ixxoid/dactyl-keyboard/resources/keyb_complete_dsa_01_1.jpg

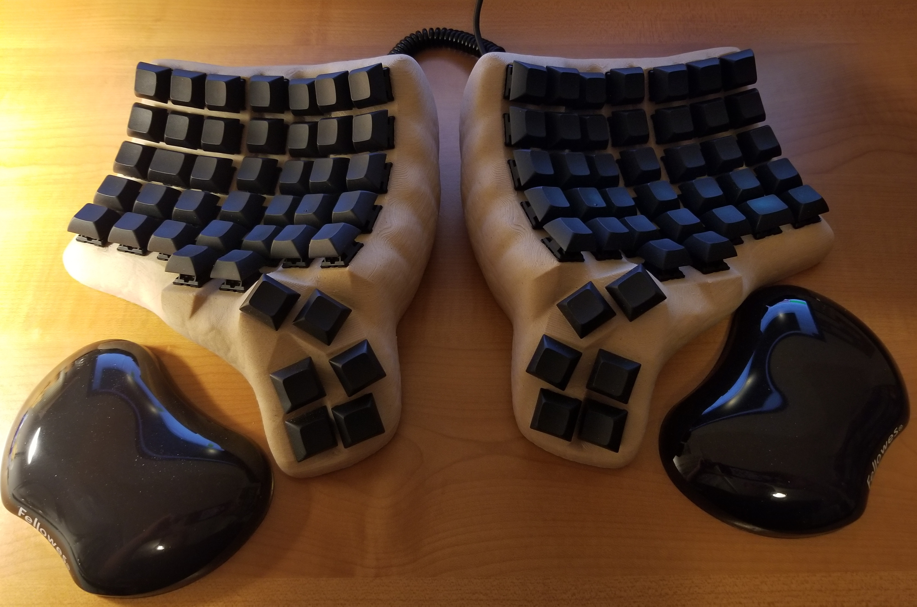
resources/keyb_complete_dsa_01_1.jpg
