ixxoid/dactyl-keyboard/resources/low_profile_preview.png

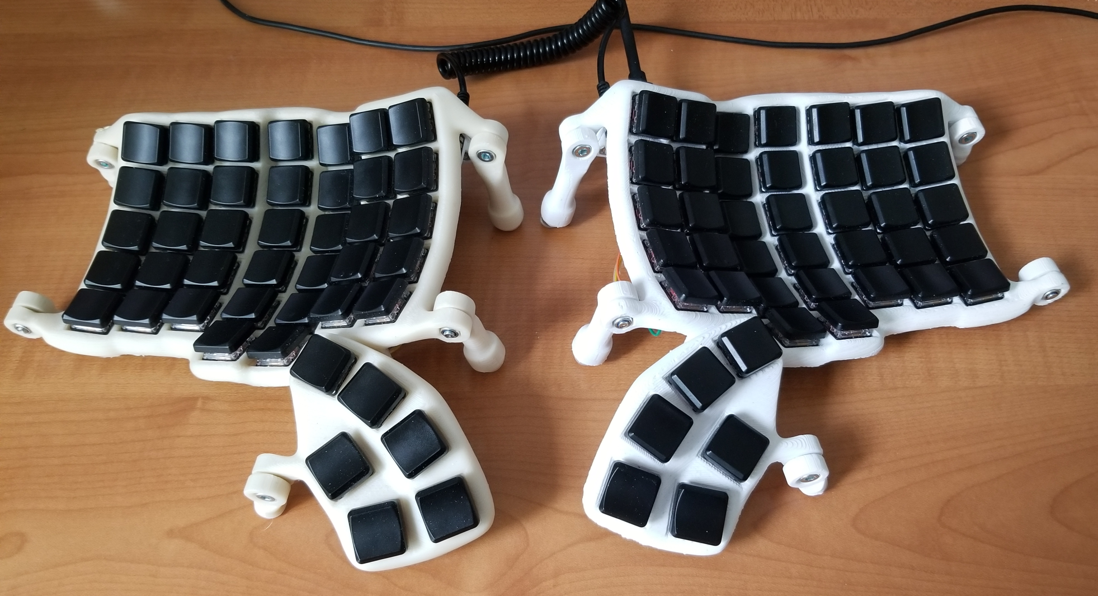
resources/low_profile_preview.png
