ixxoid/dactyl-keyboard/resources/sdds_mount_cad.png

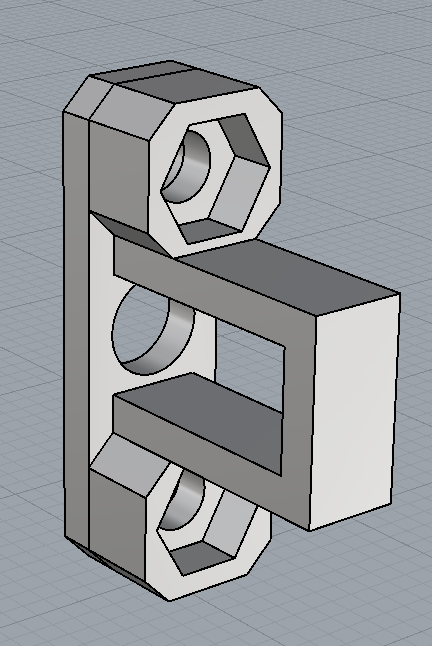
resources/sdds_mount_cad.png
